jwcxz/ACRIS/boards/prj/commbrd/commbrd.png

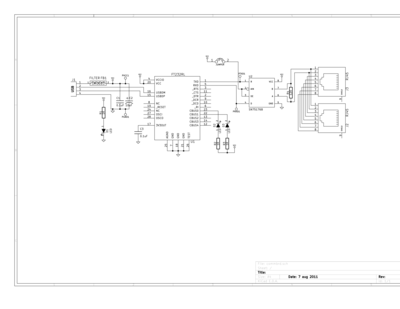
boards/prj/commbrd/commbrd.png
