jwcxz/ACRIS/boards/prj/commdngl/commdngl-brd.png

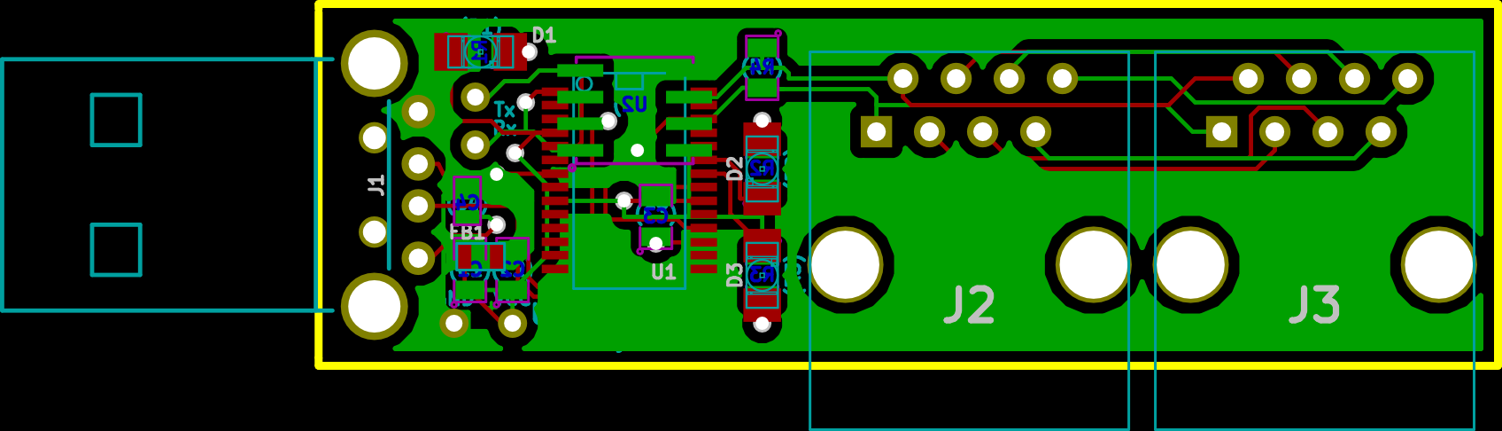
boards/prj/commdngl/commdngl-brd.png
