jwcxz/ACRIS/boards/prj/ledctrlr/ledctrlr-3d.png

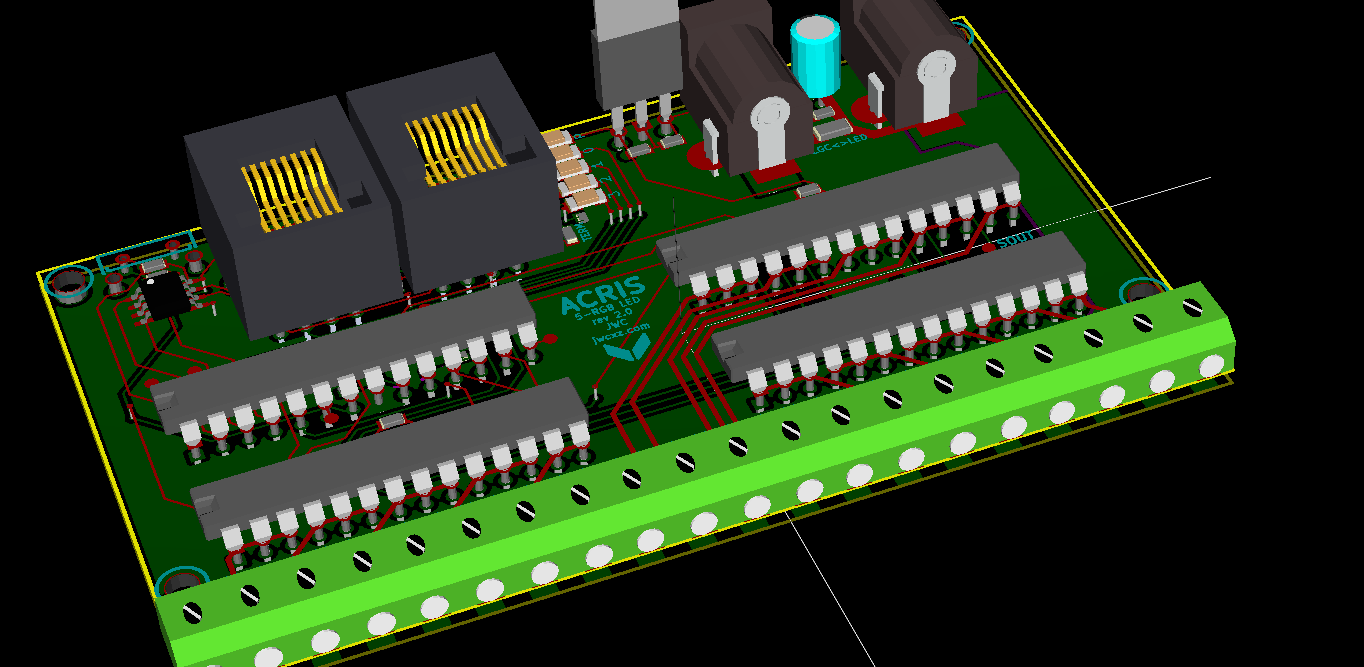
boards/prj/ledctrlr/ledctrlr-3d.png
