jwcxz/ACRIS/boards/prj/ledctrlr/ledctrlr-brd.png

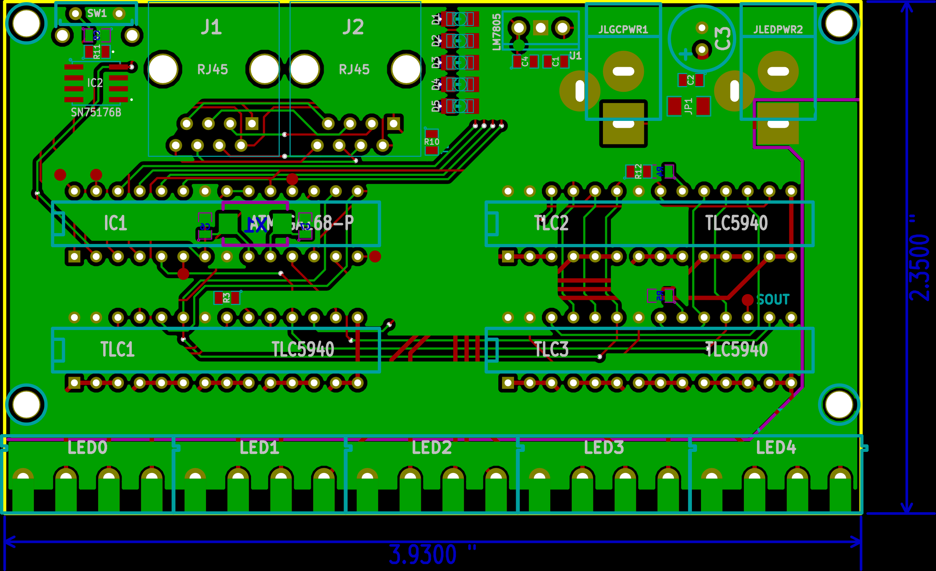
boards/prj/ledctrlr/ledctrlr-brd.png
