jwcxz/ACRIS/boards/prj/commbrd/commbrd.sch

## KiCad design boards/prj/commbrd/commbrd.sch (2011-08-11)

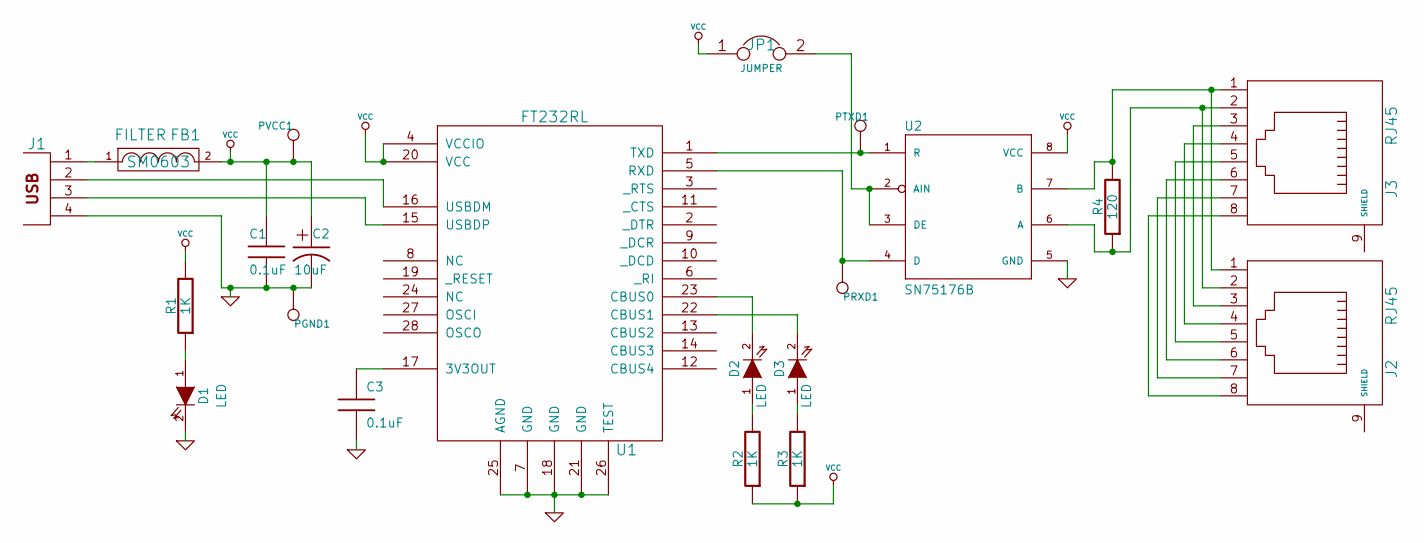
[picture p18: schematic commbrd.sch]

Parts:
C1, C3: 0.1uF; SM0805; Part CC0805ZRY5V9BB104; DigikeyPart 311-1361-1-ND
C2: 10uF; SM0805; Part TPSA106M010R1800; DigikeyPart 478-4086-1-ND
D1: LED; SM1206; Part APT3216SRCPRV; DigikeyPart 754-1142-1-ND
D2, D3: LED; LED-1206; Part APT3216SGC; DigikeyPart 754-1141-1-ND
FB1: FILTER; SM0603; Part MMZ1608D220C; DigikeyPart 445-6406-1-ND
J1: USB_2; USB_MINI_A; Part 896-43-005-00-100001; DigikeyPart ED90342CT-ND
J2: RJ45; RJ45_8
J3: RJ45; RJ45_8; Part 95501-2882; DigikeyPart WM5572-ND
JP1: JUMPER; SM1206; Part N/A; DigikeyPart N/A
PGND1: CONN_1; SIL-1; Part N/A; DigikeyPart N/A
PRXD1: CONN_1; SIL-1; Part N/A; DigikeyPart N/A
PTXD1: CONN_1; SIL-1; Part N/A; DigikeyPart N/A
PVCC1: CONN_1; SIL-1; Part N/A; DigikeyPart N/A
R1, R2, R3: 1K; SM0805; Part RMCF0805JT1K00; DigikeyPart RMCF0805JT1K00CT-ND
R4: 120; SM0805; Part RMCF0805JT120R; DigikeyPart RMCF0805JT120RCT-ND
U1: FT232RL; SSOP28; Part FT232RL-REEL; DigikeyPart 768-1007-1-ND
U2: SN75176B; SOIC8; Part SN75176BPSR; DigikeyPart 296-27995-1-ND

Connections:
GND: C1.2, C2.2, C3.2, D1.2 (K), J1.4, PGND1.1, U1.7 (GND), U1.18 (GND), U1.21 (GND), U1.25 (AGND), U1.26 (TEST), U2.5 (GND)
unnamed: C3.1, U1.17 (3V3OUT)
unnamed: D1.1 (A), R1.1
unnamed: D2.1 (A), R2.2
unnamed: D2.2 (K), U1.23 (CBUS0)
unnamed: D3.1 (A), R3.2
unnamed: D3.2 (K), U1.22 (CBUS1)
unnamed: FB1.1, J1.1
unnamed: J1.2, U1.16 (USBDM)
unnamed: J1.3, U1.15 (USBDP)
unnamed: J2.1, J3.1, R4.2, U2.7 (B)
unnamed: J2.2, J3.2, R4.1, U2.6 (A)
unnamed: J2.3, J3.3
unnamed: J2.4, J3.4
unnamed: J2.5, J3.5
unnamed: J2.6, J3.6
unnamed: J2.7, J3.7
unnamed: J2.8, J3.8
unnamed: JP1.2, U2.2 (AIN), U2.3 (DE)
unnamed: PRXD1.1, U1.5 (RXD), U2.4 (D)
unnamed: PTXD1.1, U1.1 (TXD), U2.1 (R)
VCC: C1.1, C2.1, FB1.2, JP1.1, PVCC1.1, R1.2, R2.1, R3.1, U1.4 (VCCIO), U1.20 (VCC), U2.8 (VCC)
