jwcxz/ACRIS/boards/prj/ecomm/ecomm.sch

## KiCad design boards/prj/ecomm/ecomm.sch (2012-06-20)

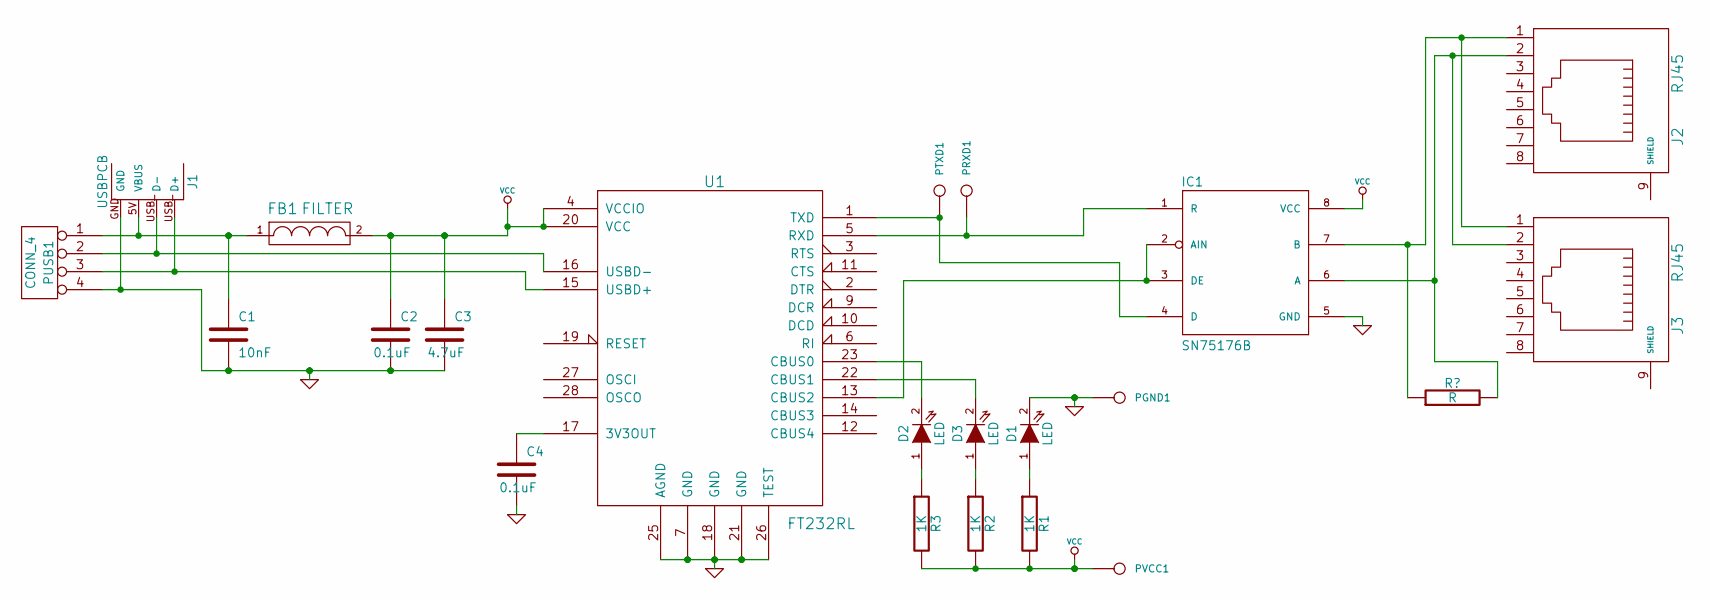
[picture p19: schematic ecomm.sch]

Parts:
C1: 10nF; SM0805
C2: 0.1uF; SM0805
C3: 4.7uF; SM0805
C4: 0.1uF; SM0603
D1, D2, D3: LED; LED-1206
FB1: FILTER; SM0603
IC1: SN75176B; DIL8
J1: USBPCB; SparkFun-USB-A-PCB
J2, J3: RJ45
PGND1: CONN_1; SIL-1
PRXD1: CONN_1; SIL-1
PTXD1: CONN_1; SIL-1
PUSB1: CONN_4; SIL-4
PVCC1: CONN_1; SIL-1
R1, R2, R3: 1K; SM0805
U1: FT232RL; SSOP28

Connections:
GND: C1.2, C2.2, C3.2, C4.2, D1.2 (K), IC1.5 (GND), J1.GND, PGND1.1, PUSB1.4, U1.7 (GND), U1.18 (GND), U1.21 (GND), U1.25 (AGND), U1.26 (TEST)
unnamed: C1.1, FB1.1, J1.5V (VBUS), PUSB1.1
unnamed: C4.1, U1.17 (3V3OUT)
unnamed: D1.1 (A), R1.1
unnamed: D2.1 (A), R3.1
unnamed: D2.2 (K), U1.23 (CBUS0)
unnamed: D3.1 (A), R2.1
unnamed: D3.2 (K), U1.22 (CBUS1)
unnamed: IC1.1 (R), PRXD1.1, U1.5 (RXD)
unnamed: IC1.2 (AIN), IC1.3 (DE), U1.13 (CBUS2)
unnamed: IC1.4 (D), PTXD1.1, U1.1 (TXD)
unnamed: IC1.6 (A), J2.2, J3.2
unnamed: IC1.7 (B), J2.1, J3.1
unnamed: J1.USB_ (D+), PUSB1.2, PUSB1.3, U1.15 (USBD+), U1.16 (USBD-)
VCC: C2.1, C3.1, FB1.2, IC1.8 (VCC), PVCC1.1, R1.2, R2.2, R3.2, U1.4 (VCCIO), U1.20 (VCC)
