jwcxz/ACRIS/boards/prj/ledctrlr/ledctrlr.sch

## KiCad design boards/prj/ledctrlr/ledctrlr.sch (2013-10-13)

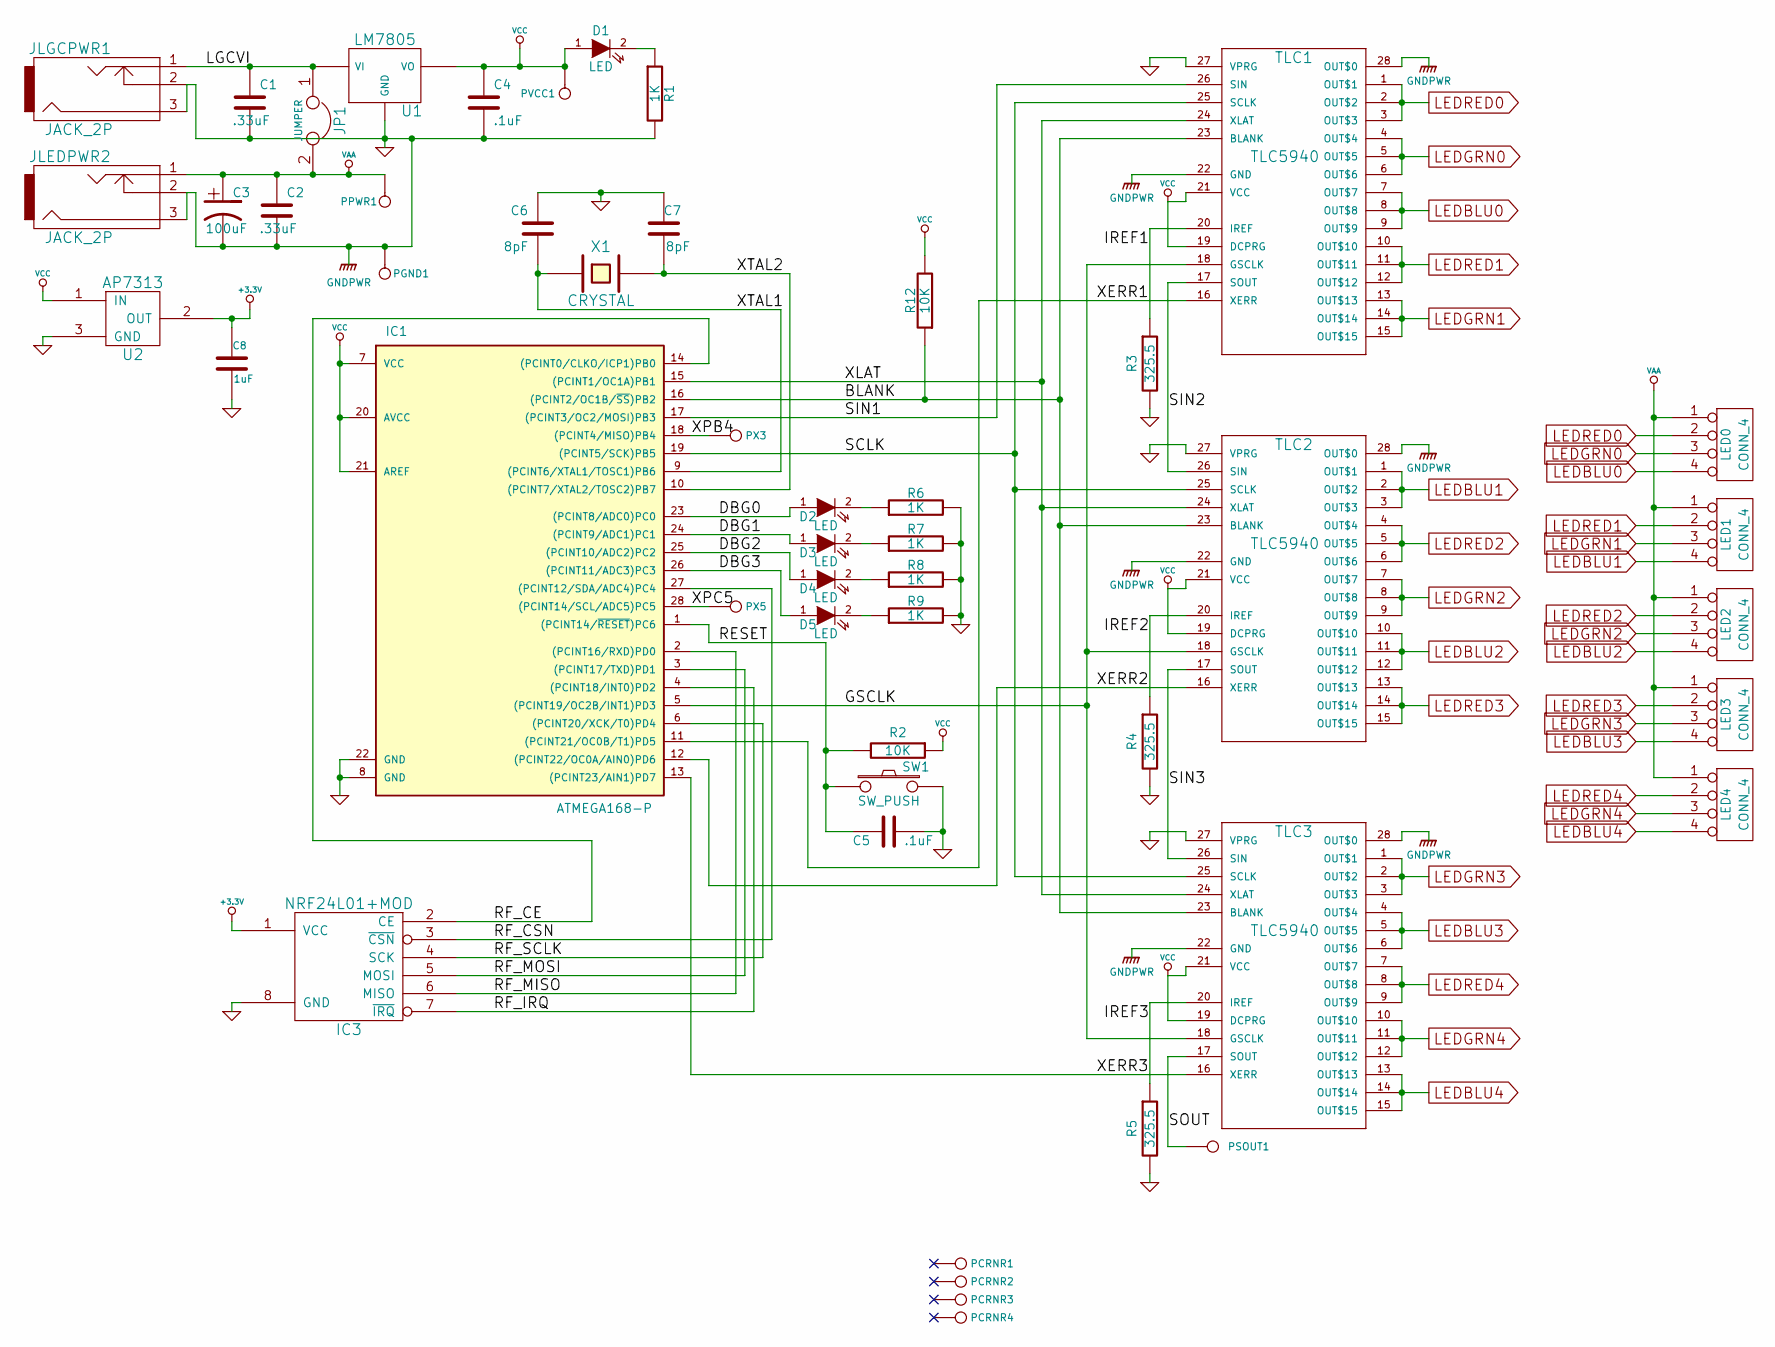
[picture p20: schematic ledctrlr.sch]

Parts:
C1, C2: .33uF; SM0805; Part C2012X7R1C334K/1.25; DigikeyPart 445-1356-1-ND
C3: 100uF; Elko_vert_DM7-5_RM2-5; Part ESK107M025AE3AA; DigikeyPart 399-6103-ND
C4, C5: .1uF; SM0805; Part CC0805ZRY5V9BB104; DigikeyPart 311-1361-1-ND
C6, C7: 8pF; SM0805; Part CC0805DRNPO9BN8R0; DigikeyPart 311-1097-1-ND
C8: 1uF; SM0805
D1: LED; LED-1206-3D; Part APT3216SRCPRV; DigikeyPart 754-1142-1-ND
D2, D3, D4, D5: LED; LED-1206-3D; Part APT3216SGC; DigikeyPart 754-1141-1-ND
IC1: ATMEGA168-P; DIP-28__300; Part ATMEGA168-20PU; DigikeyPart ATMEGA168-20PU-ND
IC3: NRF24L01+MOD; NRF24LO1+MOD_GRN
JLEDPWR2: JACK_2P; JACK_ALIM; Part PJ-202A; DigikeyPart CP-202A-ND
JLGCPWR1: JACK_2P; JACK_ALIM; Part PJ-202A; DigikeyPart CP-202A-ND
JP1: JUMPER; SM1206; Part N/A; DigikeyPart N/A
LED0, LED2, LED3, LED4: CONN_4; OSTTA040161p; Part OSTTA040161; DigikeyPart ED2563-ND
LED1: CONN_4; OSTTA040161p; Part OSTTA040161; Digikey ED2563-ND
PCRNR1, PCRNR2, PCRNR3, PCRNR4: CONN_1; screw; Part N/A; DigikeyPart N/A
PGND1: CONN_1; PAD; Part N/A; DigikeyPart N/A
PPWR1: CONN_1; PAD
PSOUT1: CONN_1; PAD; Part N/A; DigikeyPart N/A
PVCC1: CONN_1; PAD
PX3, PX5: CONN_1; PAD; Part N/A; DigikeyPart N/A
R1, R6, R7, R8, R9: 1K; SM0805; Part RMCF0805JT1K00; DigikeyPart RMCF0805JT1K00CT-ND
R2, R12: 10K; SM0805; Part RMCF0805JT10K0; DigikeyPart RMCF0805JT10K0CT-ND
R3, R4, R5: 325.5; SM0805; Part RMCF0805JT330R; DigikeyPart RMCF0805JT330RCT-ND
SW1: SW_PUSH; PUSH_SW; Part FSMRA2JH; DigikeyPart 450-1662-ND
TLC1, TLC2, TLC3: TLC5940; DIP-28__300; Part TLC5940NT; DigikeyPart 296-17732-5-ND
U1: LM7805; LM78XXV-3D; Part LM7805CT; DigikeyPart LM7805CT-ND
U2: AP7313; SOT23; Part AP7313-33SRG-7; DigikeyPart AP7313-33SRG-7DICT-ND
X1: CRYSTAL; Crystal_FOX-FE_SMD_RevA_09Aug2010; Part NX8045GB-20.000000MHZ; DigikeyPart 644-1026-1-ND

Connections:
+3.3V: C8.1, IC3.1 (VCC), U2.2 (OUT)
BLANK: IC1.16 ((PCINT2/OC1B/~SS~)PB2), R12.1, TLC1.23 (BLANK), TLC2.23 (BLANK), TLC3.23 (BLANK)
DBG0: D2.1 (A), IC1.23 ((PCINT8/ADC0)PC0)
DBG1: D3.1 (A), IC1.24 ((PCINT9/ADC1)PC1)
DBG2: D4.1 (A), IC1.25 ((PCINT10/ADC2)PC2)
DBG3: D5.1 (A), IC1.26 ((PCINT11/ADC3)PC3)
GND: C1.2, C2.2, C3.2, C4.2, C5.2, C6.2, C7.2, C8.2, IC1.8 (GND), IC1.22 (GND), IC3.8 (GND), JLEDPWR2.2, JLEDPWR2.3, JLGCPWR1.2, JLGCPWR1.3, PGND1.1, R1.2, R3.2, R4.2, R5.2, R6.2, R7.2, R8.2, R9.2, SW1.2, TLC1.22 (GND), TLC1.27 (VPRG), TLC1.28 (OUT$0), TLC2.22 (GND), TLC2.27 (VPRG), TLC2.28 (OUT$0), TLC3.22 (GND), TLC3.27 (VPRG), TLC3.28 (OUT$0), U1.GND, U2.3 (GND)
GSCLK: IC1.5 ((PCINT19/OC2B/INT1)PD3), TLC1.18 (GSCLK), TLC2.18 (GSCLK), TLC3.18 (GSCLK)
IREF1: R3.1, TLC1.20 (IREF)
IREF2: R4.1, TLC2.20 (IREF)
IREF3: R5.1, TLC3.20 (IREF)
LEDBLU0: LED0.4, TLC1.7 (OUT$7), TLC1.8 (OUT$8), TLC1.9 (OUT$9)
LEDBLU1: LED1.4, TLC2.1 (OUT$1), TLC2.2 (OUT$2), TLC2.3 (OUT$3)
LEDBLU2: LED2.4, TLC2.10 (OUT$10), TLC2.11 (OUT$11), TLC2.12 (OUT$12)
LEDBLU3: LED3.4, TLC3.4 (OUT$4), TLC3.5 (OUT$5), TLC3.6 (OUT$6)
LEDBLU4: LED4.4, TLC3.13 (OUT$13), TLC3.14 (OUT$14), TLC3.15 (OUT$15)
LEDGRN0: LED0.3, TLC1.4 (OUT$4), TLC1.5 (OUT$5), TLC1.6 (OUT$6)
LEDGRN1: LED1.3, TLC1.13 (OUT$13), TLC1.14 (OUT$14), TLC1.15 (OUT$15)
LEDGRN2: LED2.3, TLC2.7 (OUT$7), TLC2.8 (OUT$8), TLC2.9 (OUT$9)
LEDGRN3: LED3.3, TLC3.1 (OUT$1), TLC3.2 (OUT$2), TLC3.3 (OUT$3)
LEDGRN4: LED4.3, TLC3.10 (OUT$10), TLC3.11 (OUT$11), TLC3.12 (OUT$12)
LEDRED0: LED0.2, TLC1.1 (OUT$1), TLC1.2 (OUT$2), TLC1.3 (OUT$3)
LEDRED1: LED1.2, TLC1.10 (OUT$10), TLC1.11 (OUT$11), TLC1.12 (OUT$12)
LEDRED2: LED2.2, TLC2.4 (OUT$4), TLC2.5 (OUT$5), TLC2.6 (OUT$6)
LEDRED3: LED3.2, TLC2.13 (OUT$13), TLC2.14 (OUT$14), TLC2.15 (OUT$15)
LEDRED4: LED4.2, TLC3.7 (OUT$7), TLC3.8 (OUT$8), TLC3.9 (OUT$9)
LGCVI: C1.1, JLGCPWR1.1, JP1.1, U1.VI
unnamed: D1.2 (K), R1.1
unnamed: D2.2 (K), R6.1
unnamed: D3.2 (K), R7.1
unnamed: D4.2 (K), R8.1
unnamed: D5.2 (K), R9.1
RESET: C5.1, IC1.1 ((PCINT14/~RESET~)PC6), R2.2, SW1.1
RF_CE: IC1.14 ((PCINT0/CLKO/ICP1)PB0), IC3.2 (CE)
RF_CSN: IC1.27 ((PCINT12/SDA/ADC4)PC4), IC3.3 (~CSN)
RF_IRQ: IC1.4 ((PCINT18/INT0)PD2), IC3.7 (~IRQ)
RF_MISO: IC1.2 ((PCINT16/RXD)PD0), IC3.6 (MISO)
RF_MOSI: IC1.3 ((PCINT17/TXD)PD1), IC3.5 (MOSI)
RF_SCLK: IC1.6 ((PCINT20/XCK/T0)PD4), IC3.4 (SCK)
SCLK: IC1.19 ((PCINT5/SCK)PB5), TLC1.25 (SCLK), TLC2.25 (SCLK), TLC3.25 (SCLK)
SIN1: IC1.17 ((PCINT3/OC2/MOSI)PB3), TLC1.26 (SIN)
SIN2: TLC1.17 (SOUT), TLC2.26 (SIN)
SIN3: TLC2.17 (SOUT), TLC3.26 (SIN)
SOUT: PSOUT1.1, TLC3.17 (SOUT)
VAA: C2.1, C3.1, JLEDPWR2.1, JP1.2, LED0.1, LED1.1, LED2.1, LED3.1, LED4.1, PPWR1.1
VCC: C4.1, D1.1 (A), IC1.7 (VCC), IC1.20 (AVCC), IC1.21 (AREF), PVCC1.1, R2.1, R12.2, TLC1.19 (DCPRG), TLC1.21 (VCC), TLC2.19 (DCPRG), TLC2.21 (VCC), TLC3.19 (DCPRG), TLC3.21 (VCC), U1.VO, U2.1 (IN)
XERR1: IC1.11 ((PCINT21/OC0B/T1)PD5), TLC1.16 (XERR)
XERR2: IC1.12 ((PCINT22/OC0A/AIN0)PD6), TLC2.16 (XERR)
XERR3: IC1.13 ((PCINT23/AIN1)PD7), TLC3.16 (XERR)
XLAT: IC1.15 ((PCINT1/OC1A)PB1), TLC1.24 (XLAT), TLC2.24 (XLAT), TLC3.24 (XLAT)
XPB4: IC1.18 ((PCINT4/MISO)PB4), PX3.1
XPC5: IC1.28 ((PCINT14/SCL/ADC5)PC5), PX5.1
XTAL1: C6.1, IC1.9 ((PCINT6/XTAL1/TOSC1)PB6), X1.1
XTAL2: C7.1, IC1.10 ((PCINT7/XTAL2/TOSC2)PB7), X1.2
