jwcxz/ACRIS/boards/prj/ledmini/ledmini.sch

## KiCad design boards/prj/ledmini/ledmini.sch (2011-11-24)

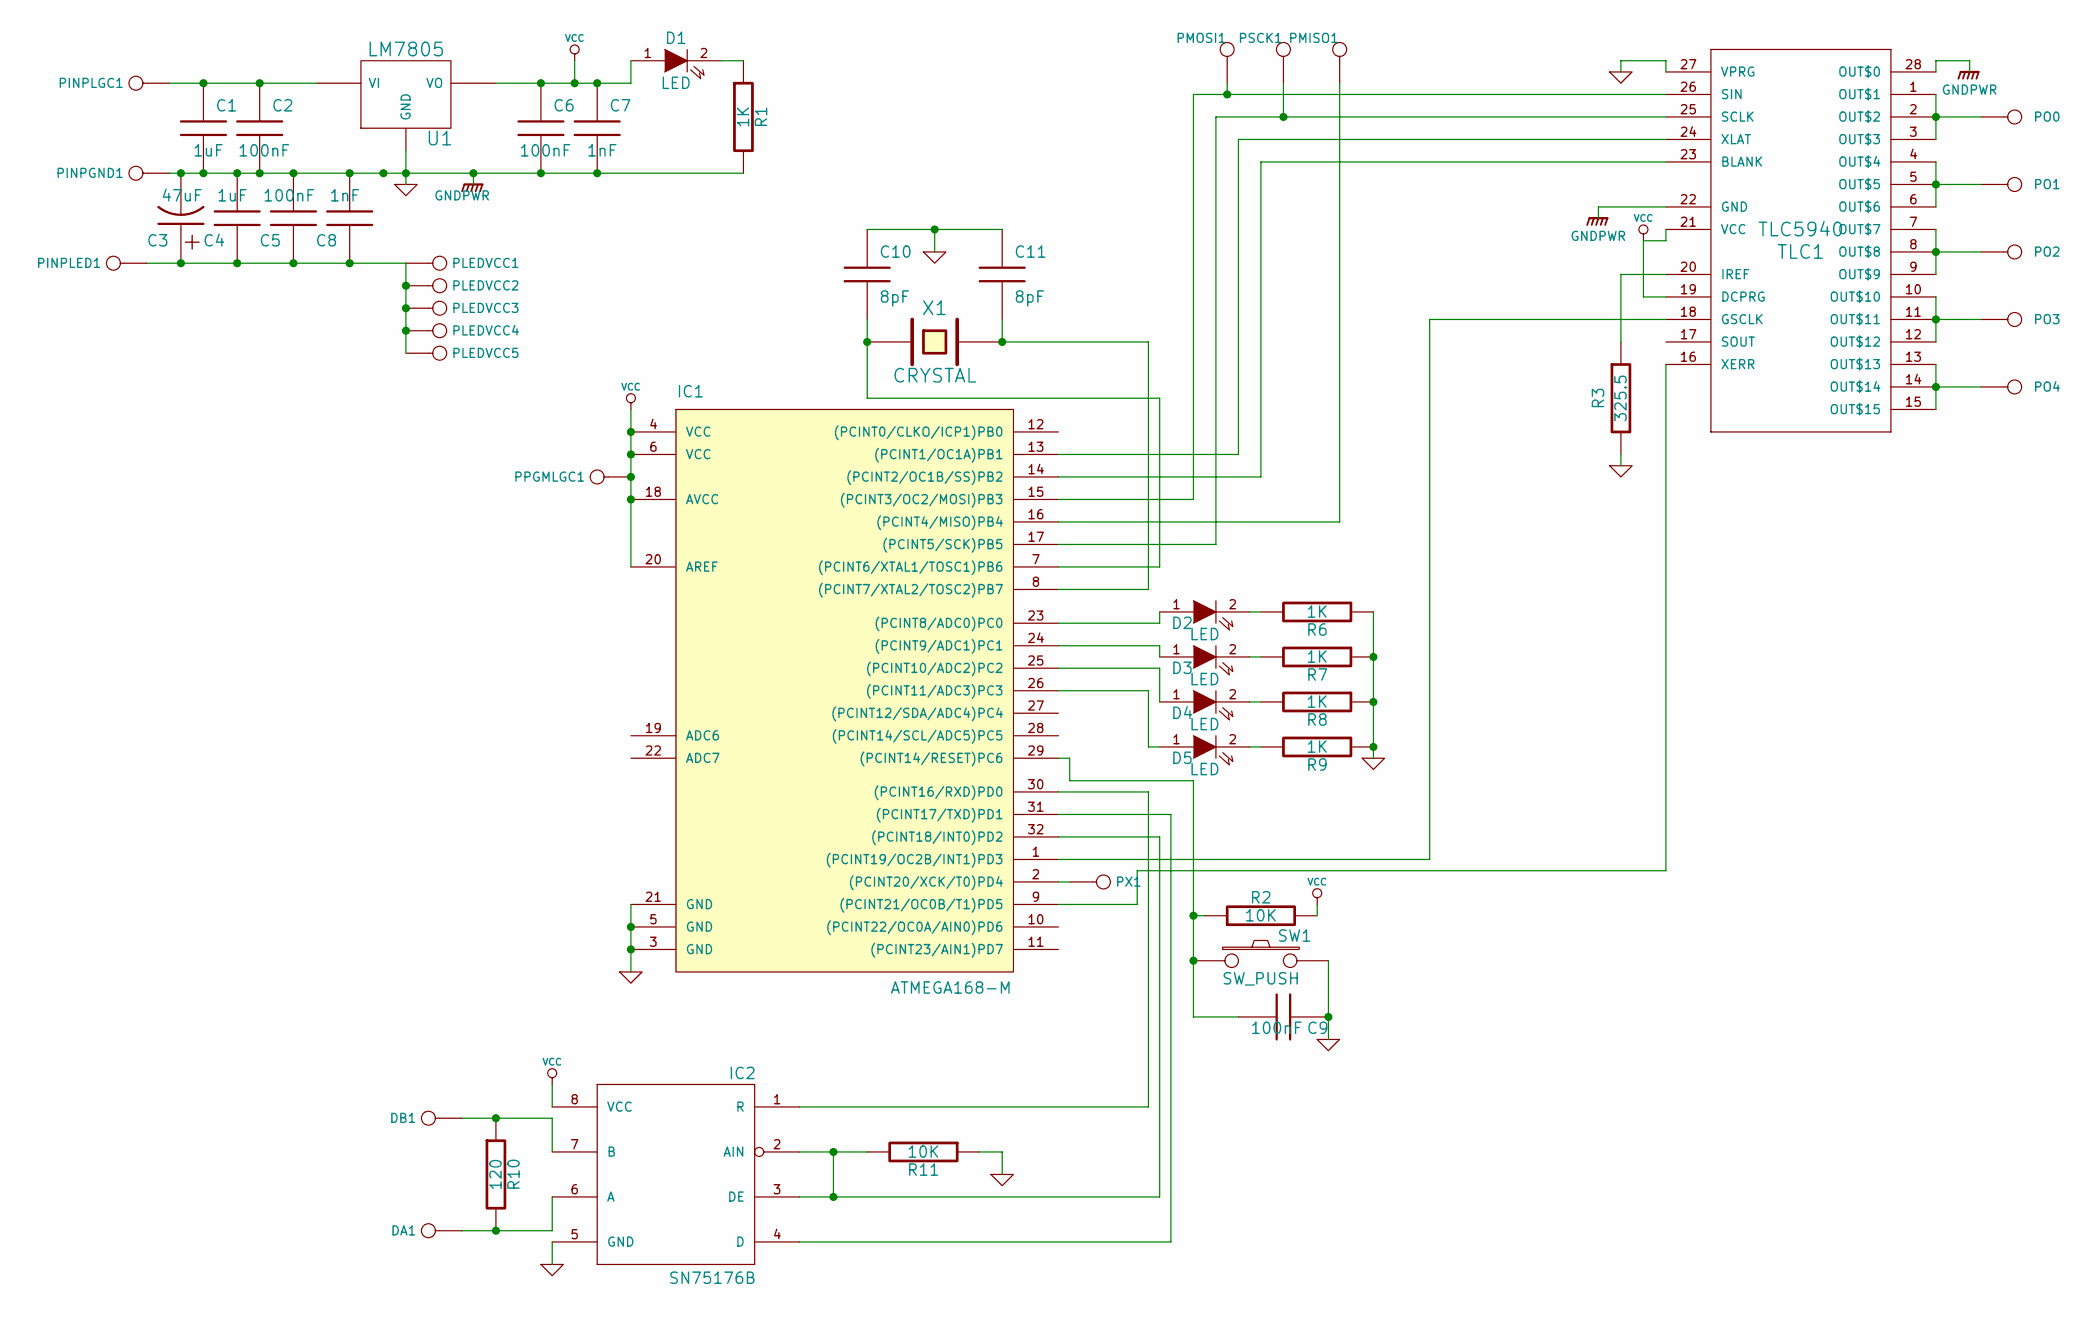
[picture p21: schematic ledmini.sch]

Parts:
C1, C4: 1uF; SM0402; Part C1005X5R0J105M; DigikeyPart 445-1415-1-ND
C2, C5, C6, C9: 100nF; SM0402; Part C1005Y5V1E104Z; DigikeyPart 445-3445-1-ND
C3: 47uF; Elko_vert_DM7-5_RM2-5; Part ECA-1CM470; DigikeyPart P5137-ND
C7, C8: 1nF; SM0402; Part C1005X7R1H102K; DigikeyPart 445-1256-1-ND
C10, C11: 8pF; SM0402; Part C1005C0G1H080D; DigikeyPart 445-4891-1-ND
D1: LED; LED-1206; Part APT3216SRCPRV; DigikeyPart 754-1142-1-ND
D2, D3, D4, D5: LED; LED-1206; Part APT3216SGC; DigikeyPart 754-1141-1-ND
DA1: CONN_1; 1pin; Part N/A; DigikeyPart N/A
DB1: CONN_1; 1pin; Part N/A; DigikeyPart N/A
IC1: ATMEGA168-M; TQFP32; Part ATMEGA168P-20AU; DigikeyPart ATMEGA168P-20AU-ND
IC2: SN75176B; SOIC8; Part SN75176BD; DigikeyPart 296-1275-5-ND
PINPGND1: CONN_1; 1pin; Part N/A; DigikeyPart N/A
PINPLED1: CONN_1; 1pin; Part N/A; DigikeyPart N/A
PINPLGC1: CONN_1; 1pin; Part N/A; DigikeyPart N/A
PLEDVCC1, PLEDVCC2, PLEDVCC3, PLEDVCC4, PLEDVCC5: CONN_1; SIL-1; Part N/A; DigikeyPart N/A
PMISO1: CONN_1; SIL-1; Part N/A; DigikeyPart N/A
PMOSI1: CONN_1; SIL-1; Part N/A; DigikeyPart N/A
PO0, PO1, PO2, PO3, PO4: CONN_1; 1pin; Part N/A; DigikeyPart N/A
PPGMLGC1: CONN_1; 1pin; Part N/A; DigikeyPart N/A
PSCK1: CONN_1; SIL-1; Part N/A; DigikeyPart N/A
PX1: CONN_1; SIL-1; Part N/A; DigikeyPart N/A
R1, R6, R7, R8, R9: 1K; SM0402; Part RMCF0402JT1K00; DigikeyPart RMCF0402JT1K00CT-ND
R2: 10K; SM0402; Part RMCF0402JT10K0; DigikeyPart RMCF0402JT10K0CT-ND
R3: 325.5; SM0402; Part P330JCT-ND; DigikeyPart ERJ-2GEJ331X
R10: 120; SM0402; Part ERJ-2GEJ121X; DigikeyPart P120JCT-ND
R11: 10K; Part RMCF0402JT10K0; DigikeyPart RMCF0402JT10K0CT-ND
SW1: SW_PUSH; PUSH_SW; Part FSMRA2JH; DigikeyPart 450-1662-ND
TLC1: TLC5940; SSOP28; Part TLC5940PWP; DigikeyPart 296-17733-5-ND
U1: LM7805; LM78XXV; Part LM7805CT; DigikeyPart LM7805CT-ND
X1: CRYSTAL; Crystal_FOX-FE_SMD_RevA_09Aug2010; Part NX8045GB-20.000000MHZ; DigikeyPart 644-1026-1-ND

Connections:
GND: C1.2, C2.2, C3.2, C4.2, C5.2, C6.2, C7.2, C8.2, C9.1, C10.1, C11.1, IC1.3 (GND), IC1.5 (GND), IC1.21 (GND), IC2.5 (GND), PINPGND1.1, R1.2, R3.2, R6.1, R7.1, R8.1, R9.1, R11.1, SW1.2, TLC1.22 (GND), TLC1.27 (VPRG), TLC1.28 (OUT$0), U1.GND
unnamed: C1.1, C2.1, PINPLGC1.1, U1.VI
unnamed: C3.1, C4.1, C5.1, C8.1, PINPLED1.1, PLEDVCC1.1, PLEDVCC2.1, PLEDVCC3.1, PLEDVCC4.1, PLEDVCC5.1
unnamed: C9.2, IC1.29 ((PCINT14/RESET)PC6), R2.1, SW1.1
unnamed: C10.2, IC1.7 ((PCINT6/XTAL1/TOSC1)PB6), X1.1
unnamed: C11.2, IC1.8 ((PCINT7/XTAL2/TOSC2)PB7), X1.2
unnamed: D1.2 (K), R1.1
unnamed: D2.1 (A), IC1.23 ((PCINT8/ADC0)PC0)
unnamed: D2.2 (K), R6.2
unnamed: D3.1 (A), IC1.24 ((PCINT9/ADC1)PC1)
unnamed: D3.2 (K), R7.2
unnamed: D4.1 (A), IC1.25 ((PCINT10/ADC2)PC2)
unnamed: D4.2 (K), R8.2
unnamed: D5.1 (A), IC1.26 ((PCINT11/ADC3)PC3)
unnamed: D5.2 (K), R9.2
unnamed: DA1.1, IC2.6 (A), R10.2
unnamed: DB1.1, IC2.7 (B), R10.1
unnamed: IC1.1 ((PCINT19/OC2B/INT1)PD3), TLC1.18 (GSCLK)
unnamed: IC1.2 ((PCINT20/XCK/T0)PD4), PX1.1
unnamed: IC1.9 ((PCINT21/OC0B/T1)PD5), TLC1.16 (XERR)
unnamed: IC1.13 ((PCINT1/OC1A)PB1), TLC1.24 (XLAT)
unnamed: IC1.14 ((PCINT2/OC1B/SS)PB2), TLC1.23 (BLANK)
unnamed: IC1.15 ((PCINT3/OC2/MOSI)PB3), PMOSI1.1, TLC1.26 (SIN)
unnamed: IC1.16 ((PCINT4/MISO)PB4), PMISO1.1
unnamed: IC1.17 ((PCINT5/SCK)PB5), PSCK1.1, TLC1.25 (SCLK)
unnamed: IC1.30 ((PCINT16/RXD)PD0), IC2.1 (R)
unnamed: IC1.31 ((PCINT17/TXD)PD1), IC2.4 (D)
unnamed: IC1.32 ((PCINT18/INT0)PD2), IC2.2 (AIN), IC2.3 (DE), R11.2
unnamed: PO0.1, TLC1.1 (OUT$1), TLC1.2 (OUT$2), TLC1.3 (OUT$3)
unnamed: PO1.1, TLC1.4 (OUT$4), TLC1.5 (OUT$5), TLC1.6 (OUT$6)
unnamed: PO2.1, TLC1.7 (OUT$7), TLC1.8 (OUT$8), TLC1.9 (OUT$9)
unnamed: PO3.1, TLC1.10 (OUT$10), TLC1.11 (OUT$11), TLC1.12 (OUT$12)
unnamed: PO4.1, TLC1.13 (OUT$13), TLC1.14 (OUT$14), TLC1.15 (OUT$15)
unnamed: R3.1, TLC1.20 (IREF)
VCC: C6.1, C7.1, D1.1 (A), IC1.4 (VCC), IC1.6 (VCC), IC1.18 (AVCC), IC1.20 (AREF), IC2.8 (VCC), PPGMLGC1.1, R2.2, TLC1.19 (DCPRG), TLC1.21 (VCC), U1.VO
