jwcxz/ACRIS/avr/prj/ledctrlr_uart/config.h

#ifndef __CONFIG_H_
#define __CONFIG_H_


#include "config_top.h"
#include "pins.h"


// UART config
#define UART_PRESCALER  259
#define UART_DBL        1
#define UART_PARITY     0

#define UART_RX_BUFSZ   64
#define UART_TX_BUFSZ   1


#endif
