jwcxz/ACRIS/avr/ledctrlr/uart.c

/* A C R I S   P R O J E C T ********
 * LED Controller                   *
 * http://jwcxz.com/projects/acris  *
 *                                  *
 * J. Colosimo -- http://jwcxz.com/ *
 *                                  *
 * UART interface                   *
 ************************************/

#include "uart.h"
#include "dbgled.h"
#include "eeprom.h"

void uart_init(void) {
    // set rs485 tristate to "read"
    UARTWR_DDR |= _BV(UARTWR_PIN);
    _OFF(UARTWR_PRT, UARTWR_PIN);
    // XXX: if we ever enable transmission, we'll need to switch between "read"
    // and "write" on the interrupts
    
    uint16_t baud = get_baud();
	UBRR0H = (unsigned char) (baud>>8);
	UBRR0L = (unsigned char) baud;

    uint8_t dbl = get_baud_dbl();
    UCSR0A = ( dbl << U2X0 );
    // XXX: TXEN0 is disabled
	UCSR0B = ( _BV(RXCIE0) | _BV(RXEN0) );
	UCSR0C = ( _BV(UCSZ01) | _BV(UCSZ00) );

    // enable even parity
    UCSR0C |= _BV(UPM01);

    // reset the pointers and buffer count
	uart_rxbuf_iptr = uart_rxbuf;
	uart_rxbuf_optr = uart_rxbuf;
    uart_rxbuf_count = 0;
    /* XXX: enable with TX
	uart_txbuf_iptr = uart_txbuf;
	uart_txbuf_optr = uart_txbuf;
    */
}

uint8_t uart_rx(void) {
	unsigned char tmp;
    cli();

	while ( uart_rxbuf_count == 0 );

	tmp = *uart_rxbuf_optr;
	uart_rxbuf_count--;

	uart_rxbuf_optr++;
	if ( uart_rxbuf_optr >= uart_rxbuf + UART_RX_BUFSZ )
		uart_rxbuf_optr = uart_rxbuf;

    sei();
	return tmp;
}

uint8_t uart_data_rdy(void) {
	return ( uart_rxbuf_count );
}

/* XXX: enable with TX
void uart_tx(uint8_t data) {
	while ( uart_txbuf_count >= UART_TX_BUFSZ );

	*uart_txbuf_iptr = data;
	uart_txbuf_count++;

	uart_txbuf_iptr++;
	if ( uart_txbuf_iptr >= uart_txbuf + UART_TX_BUFSZ )
		uart_txbuf_iptr = uart_txbuf;

	_ON(UCSR0B,UDRIE0);
}
*/

/* INTERRUPT VECTORS */
ISR(USART_RX_vect) {
	unsigned char data;

    if ( UCSR0A & _BV(UPE0) ) {
        // parity error
        dbg_on(DBG_PRTYERR);
    } else {
        data = UDR0;

        if ( uart_rxbuf_count <= UART_RX_BUFSZ ) {
            *uart_rxbuf_iptr = data;
            uart_rxbuf_count++;

            uart_rxbuf_iptr++;
            if ( uart_rxbuf_iptr >= uart_rxbuf + UART_RX_BUFSZ )
                uart_rxbuf_iptr = uart_rxbuf;
        } else {
            // buffer overflow!
            // shut interrupts off until we can deplete the buffer a bit
            cli();
            rxen = 0;

            dbg_on(DBG_OVFLWERR);
        }
    }
}

/* XXX: enable with TX
ISR(USART_TX_vect) {
	if ( uart_txbuf_count > 0 ) {
        // set rs485 tristate to "write"
        _ON(UARTWR_PRT, UARTWR_PIN);

		UDR0 = *uart_txbuf_optr;
		uart_txbuf_count--;

		uart_txbuf_optr++;
		if ( uart_txbuf_optr >= uart_txbuf + UART_TX_BUFSZ )
			uart_txbuf_optr = uart_txbuf;
	} else {
		_OFF(UCSR0B, UDRIE0);
	}
}
*/
